Labsmore/Maasi/images/parts.jpg

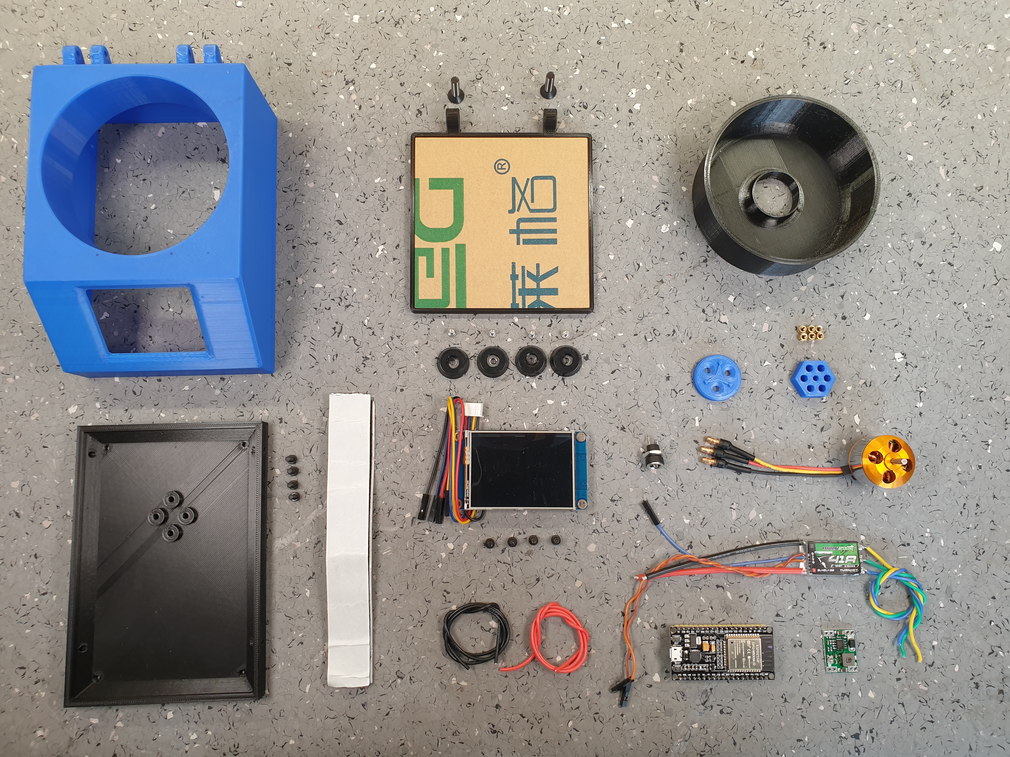
images/parts.jpg
